keebio/sinc-case/enclosed-case/Mid Layer - Rev 3-4 Left Macro.stl

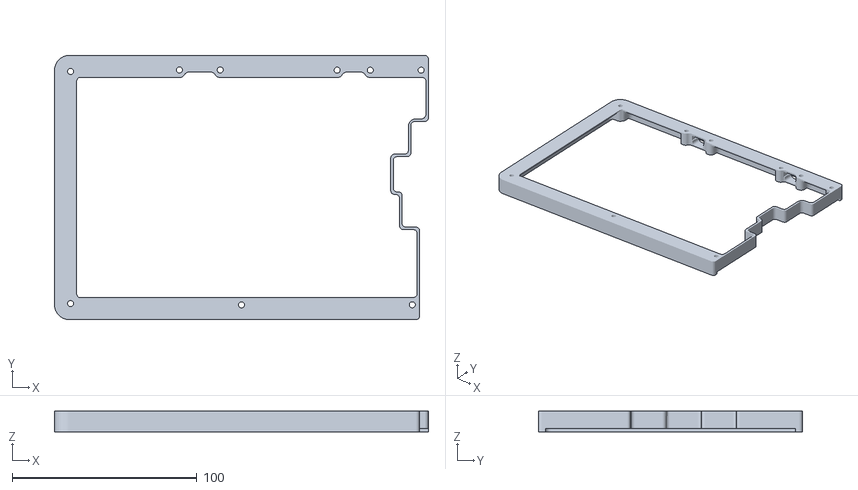
[picture p14: CAD file, 2025-05-04]
enclosed-case/Mid Layer - Rev 3-4 Left Macro.stl
202.5 x 143.1 x 11.3
