keebio/sinc-case/enclosed-case/Top Shell - Right No Right Column.stl

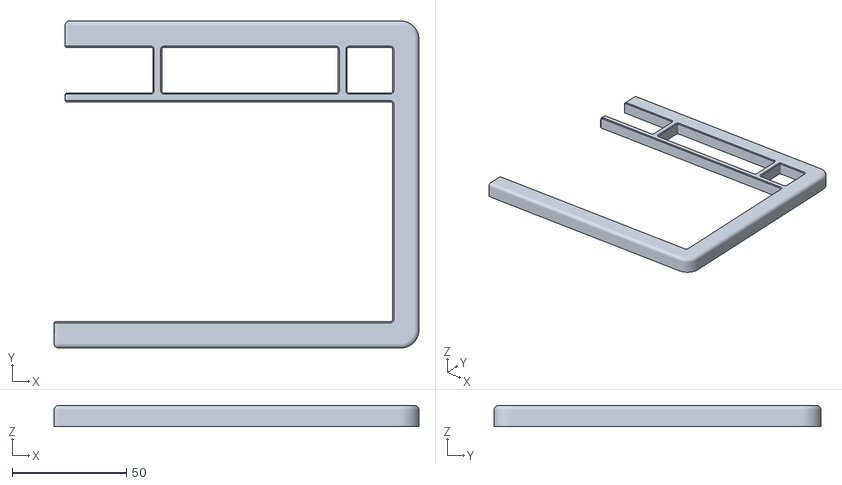
[picture p15: CAD file, 2023-09-20]
enclosed-case/Top Shell - Right No Right Column.stl
159.6 x 143.1 x 9.30
