keebio/sinc-case/Top Shell - Right.stl

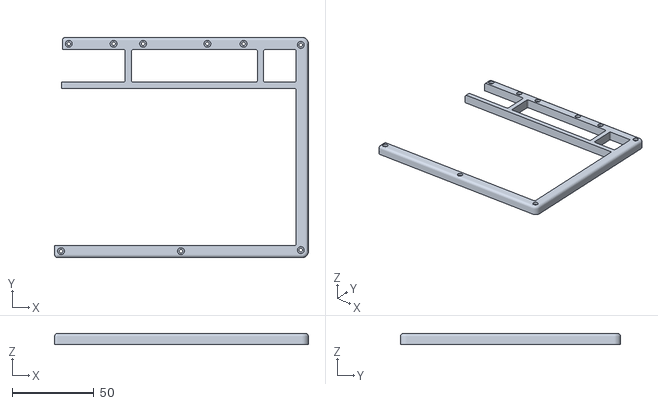
[picture p16: CAD file, 2020-12-21]
Top Shell - Right.stl
155.6 x 135.1 x 7.00
