keebio/sinc-case/enclosed-case/Mid Layer - Rev 2 Right No Right Column.stl

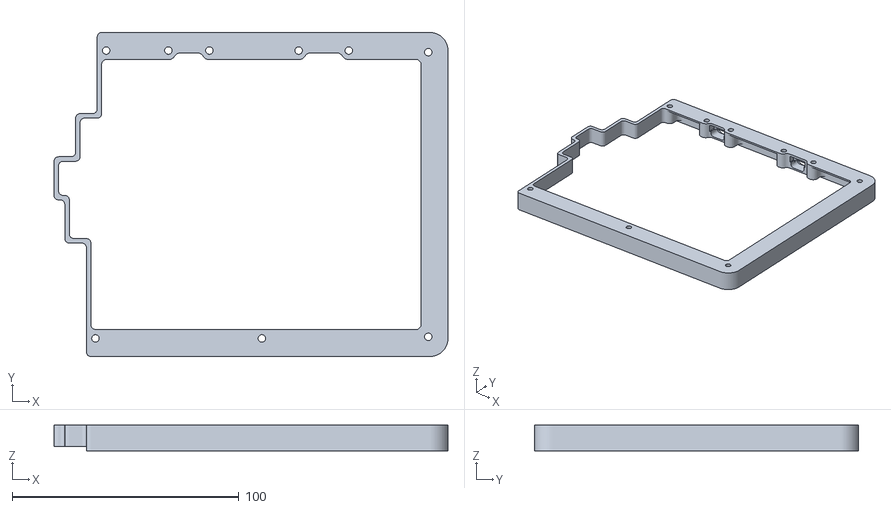
[picture p17: CAD file, 2023-09-20]
enclosed-case/Mid Layer - Rev 2 Right No Right Column.stl
173.9 x 143.1 x 11.3
