keebio/sinc-case/enclosed-case/Mid Layer - Rev 1 Right.stl

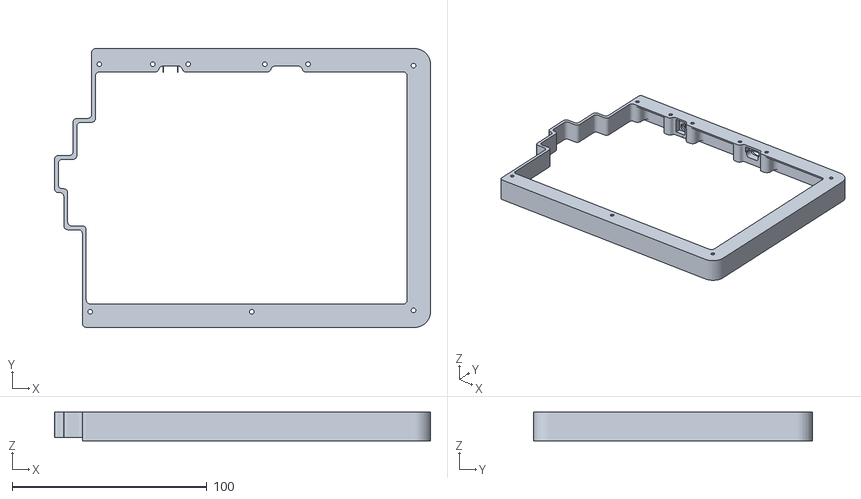
[picture p18: CAD file, 2022-04-13]
enclosed-case/Mid Layer - Rev 1 Right.stl
193.0 x 143.1 x 14.8
