keebio/sinc-case/Top Shell - Left.stl

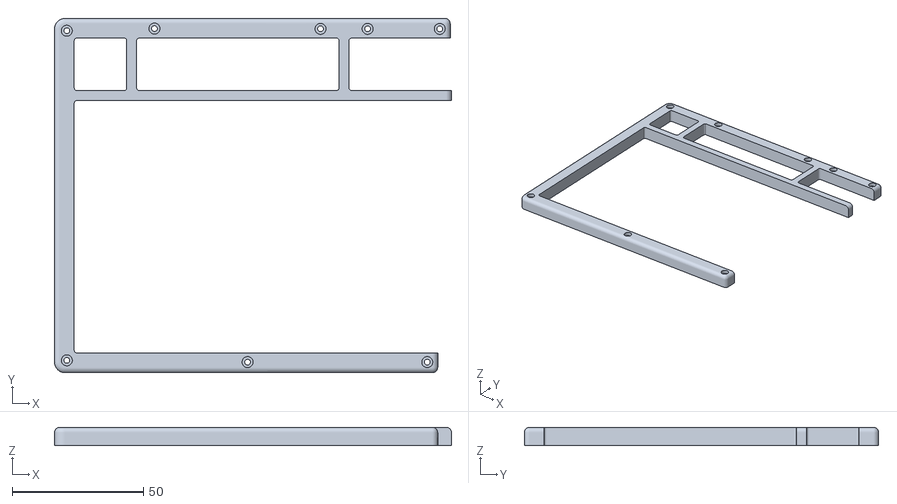
[picture p19: CAD file, 2020-12-21]
Top Shell - Left.stl
151.4 x 135.1 x 7.00
