keebio/sinc-case/enclosed-case/Mid Layer - Rev 2 Left No Macro.stl

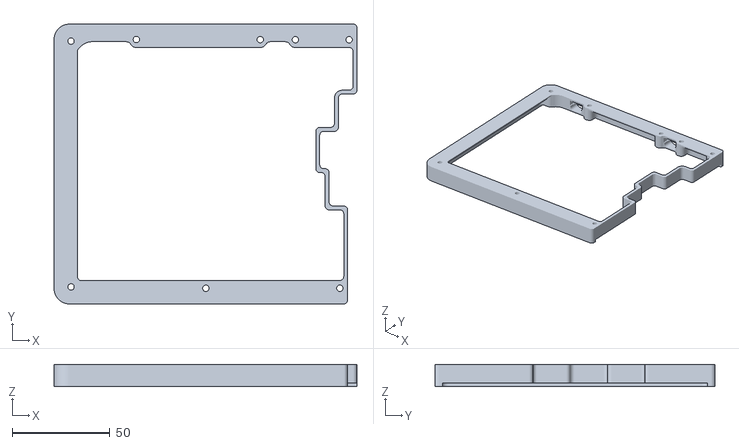
[picture p20: CAD file, 2021-10-15]
enclosed-case/Mid Layer - Rev 2 Left No Macro.stl
154.9 x 143.1 x 11.3
