keebio/sinc-case/enclosed-case/Top Shell - Right with Encoder.stl

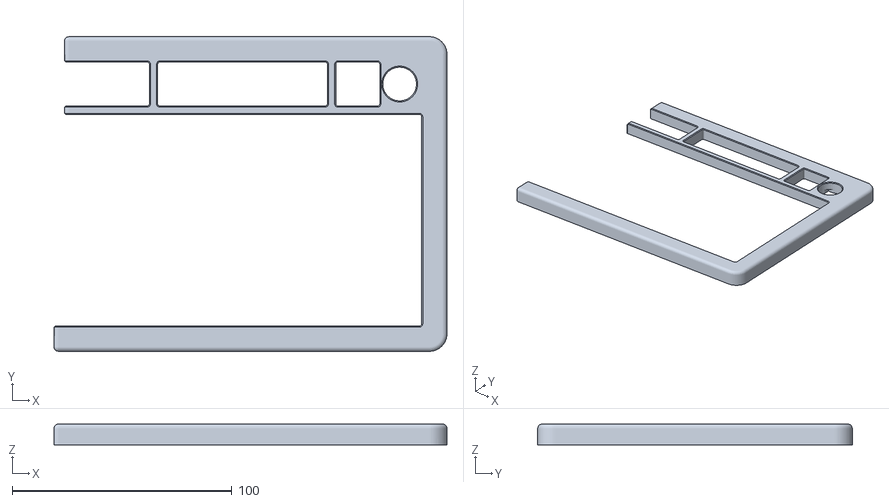
[picture p21: CAD file, 2021-10-15]
enclosed-case/Top Shell - Right with Encoder.stl
178.7 x 143.1 x 9.50
