keebio/sinc-case/Mid - Left.stl

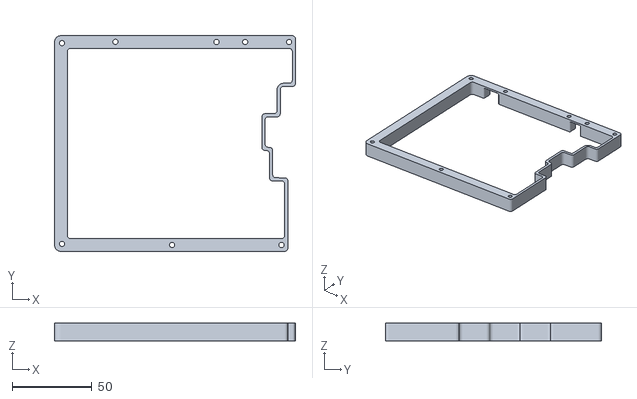
[picture p22: CAD file, 2020-07-27]
Mid - Left.stl
150.9 x 135.1 x 11.0
