keebio/sinc-case/Mid - Right.stl

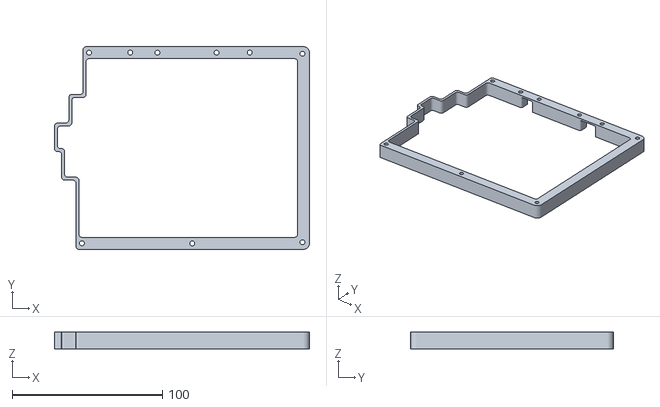
[picture p23: CAD file, 2020-07-27]
Mid - Right.stl
169.9 x 135.1 x 11.0
