keebio/sinc-case/enclosed-case/Top Shell - Left Macro.stl

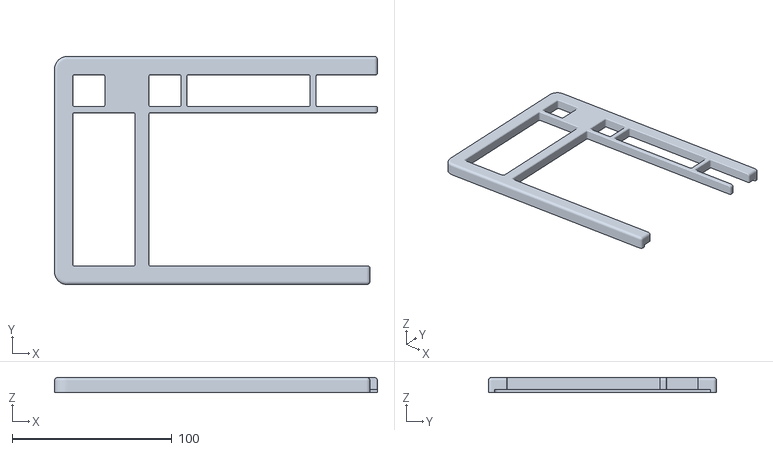
[picture p24: CAD file, 2021-10-15]
enclosed-case/Top Shell - Left Macro.stl
202.5 x 143.1 x 9.50
