keebio/sinc-case/enclosed-case/Top Shell - Left No Macro.stl

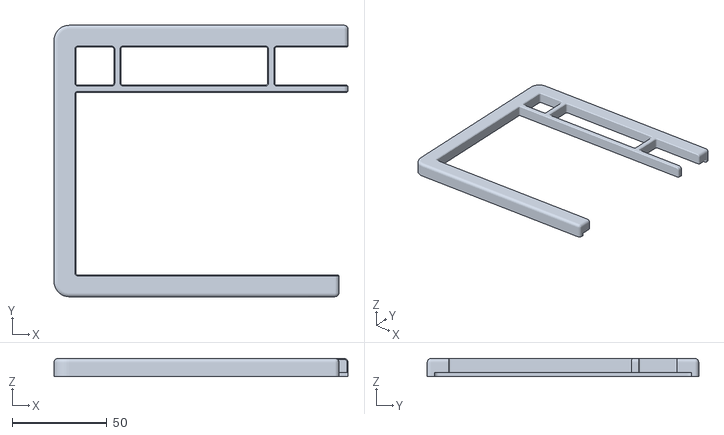
[picture p25: CAD file, 2021-10-15]
enclosed-case/Top Shell - Left No Macro.stl
154.9 x 143.1 x 9.50
