keebio/sinc-case/enclosed-case/Top Shell - Right.stl

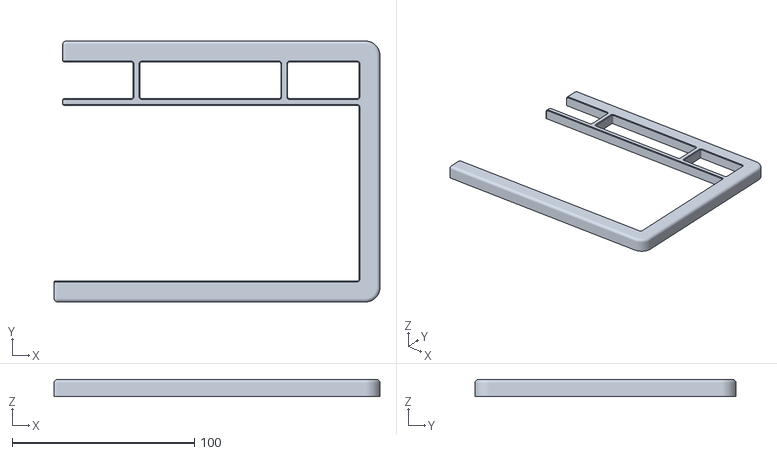
[picture p26: CAD file, 2021-10-15]
enclosed-case/Top Shell - Right.stl
178.7 x 143.1 x 9.50
