keebio/sinc-case/enclosed-case/Mid Layer - Rev 2-4 Right.stl

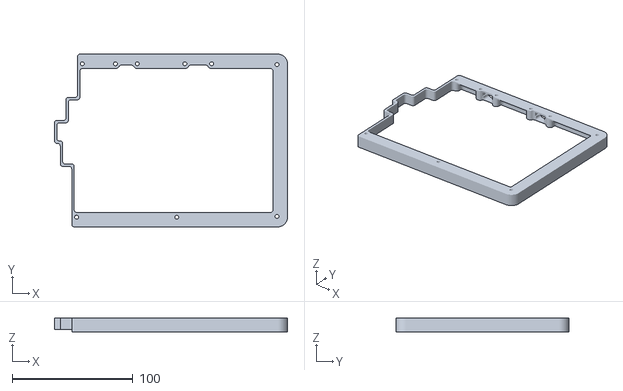
[picture p27: CAD file, 2021-08-30]
enclosed-case/Mid Layer - Rev 2-4 Right.stl
193.0 x 143.1 x 11.3
